manubompella/thingShield/thingShield-Bot/Reference/max232.png

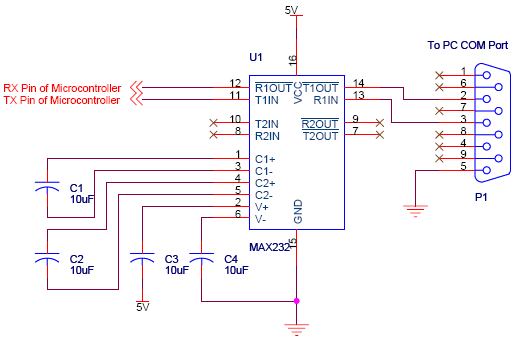
thingShield-Bot/Reference/max232.png
